LE0ST/Transmisor-FM/simulation/captures/4nec2/[2] Configuración GEOMETRY.png

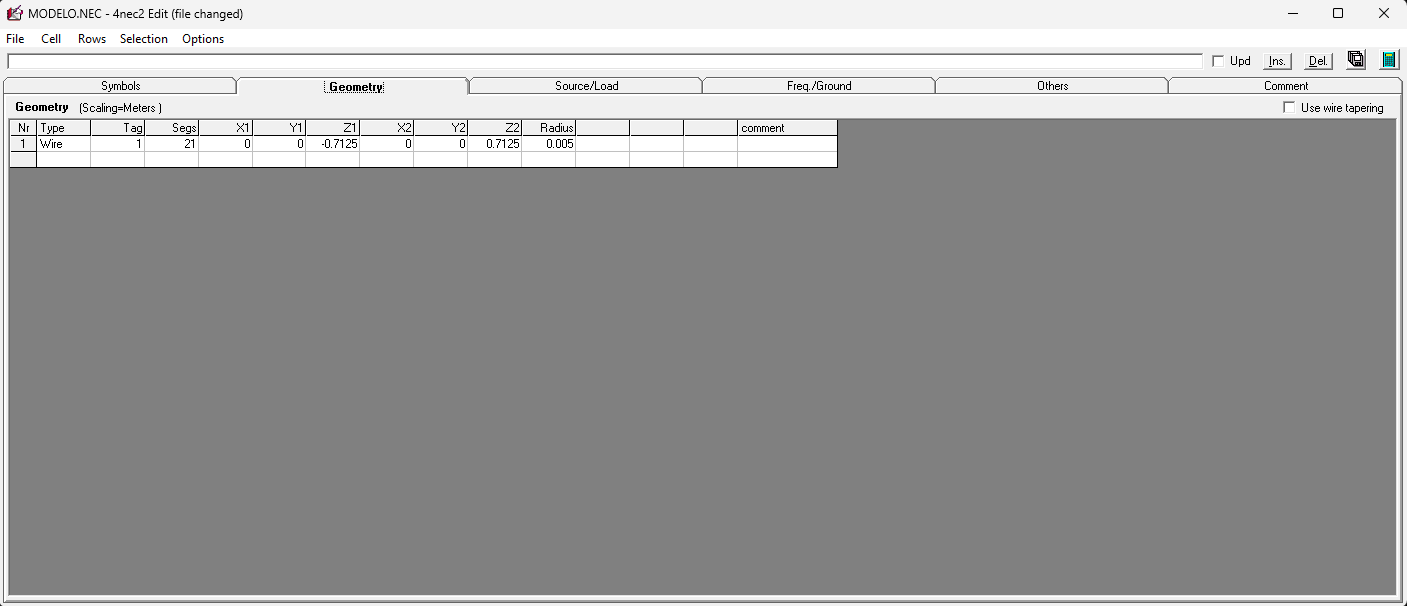
simulation/captures/4nec2/[2] Configuración GEOMETRY.png
