LE0ST/Transmisor-FM/simulation/captures/4nec2/[4] Configuración FREQ_GROUND.png

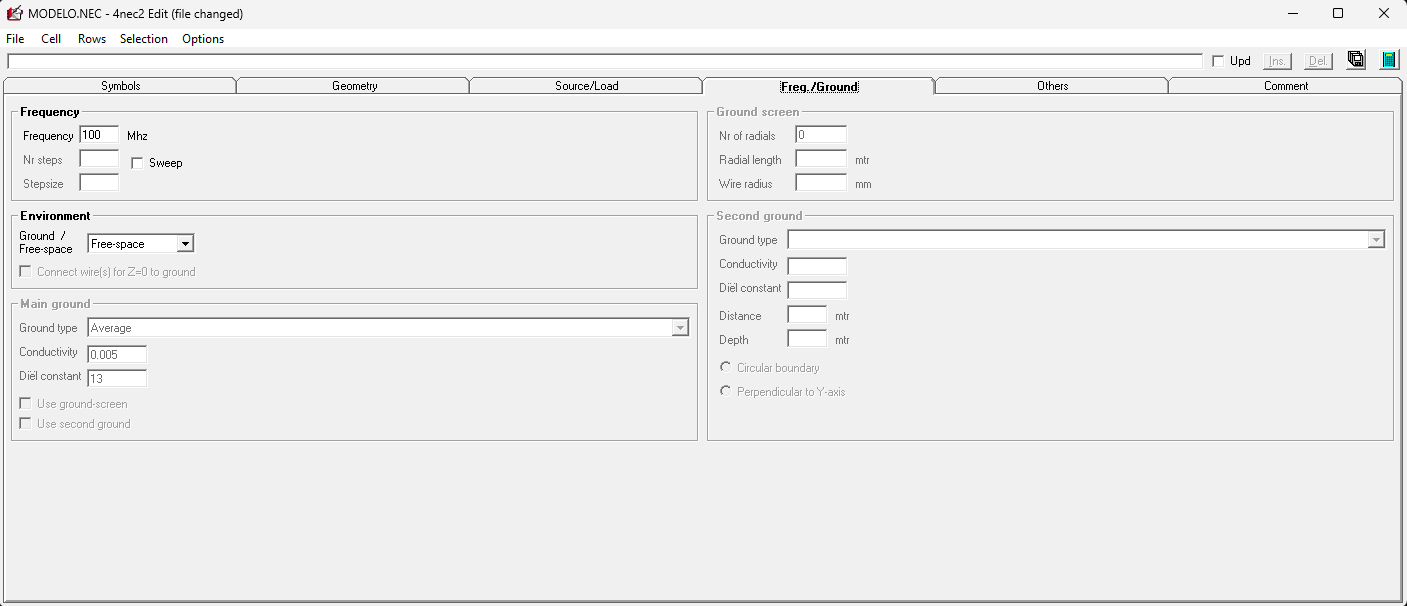
simulation/captures/4nec2/[4] Configuración FREQ_GROUND.png
