LE0ST/Transmisor-FM/simulation/captures/4nec2/[5] Modelo 3D.png

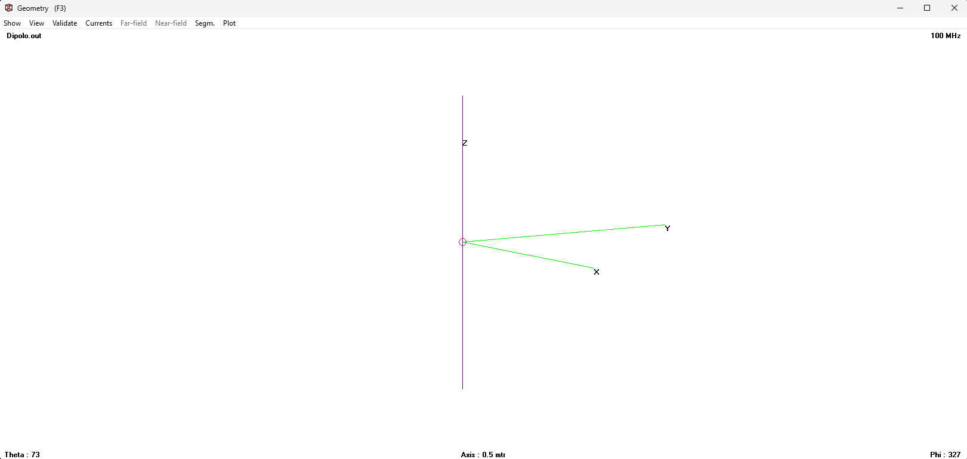
simulation/captures/4nec2/[5] Modelo 3D.png
