LE0ST/Transmisor-FM/simulation/captures/4nec2/[6] Diagrama de Radiación 2D.png

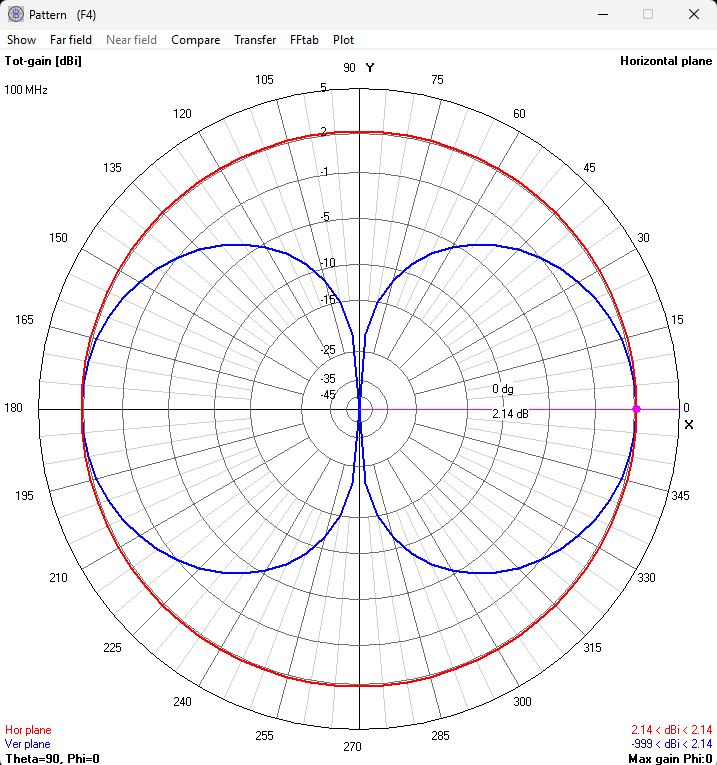
simulation/captures/4nec2/[6] Diagrama de Radiación 2D.png
