LE0ST/Transmisor-FM/simulation/captures/4nec2/[8] Respuesta SWR.png

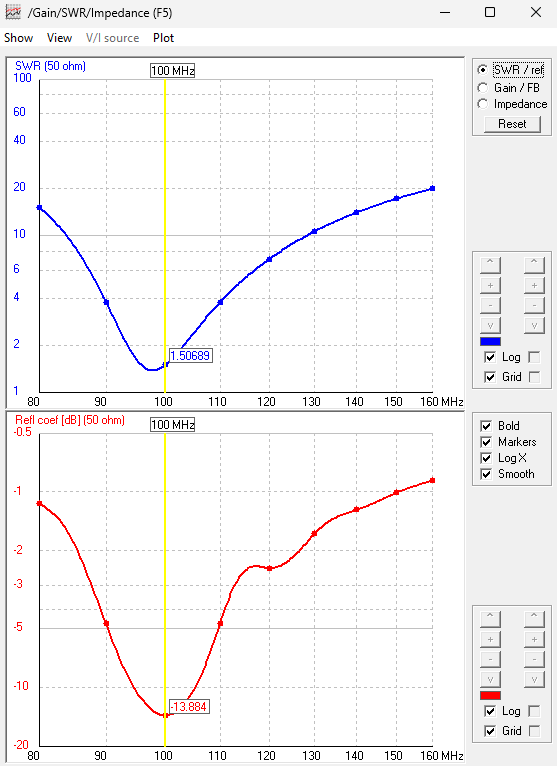
simulation/captures/4nec2/[8] Respuesta SWR.png
