LE0ST/Transmisor-FM/simulation/captures/altium_designer/[3] Altium Library Loader.png

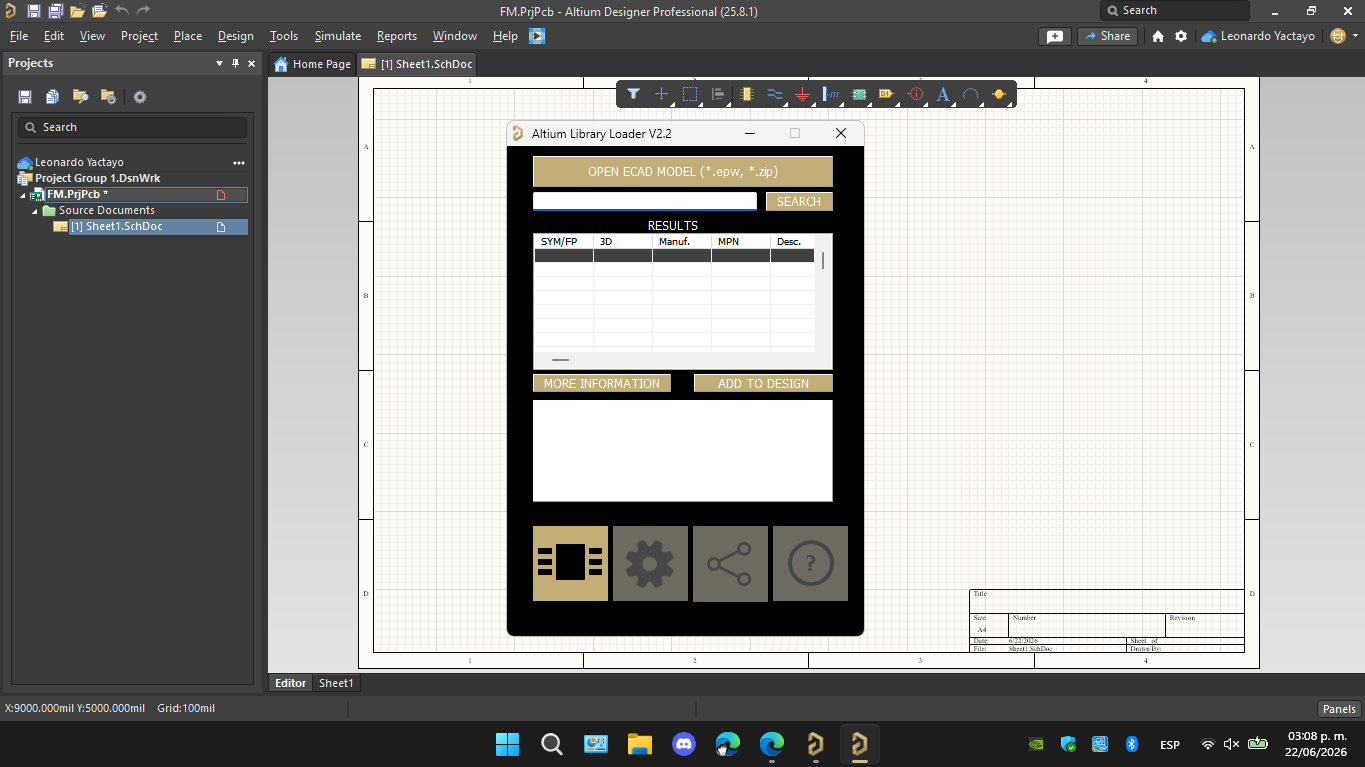
simulation/captures/altium_designer/[3] Altium Library Loader.png
