LE0ST/Transmisor-FM/simulation/captures/altium_designer/[4] Esquemático S9014 S9018.png

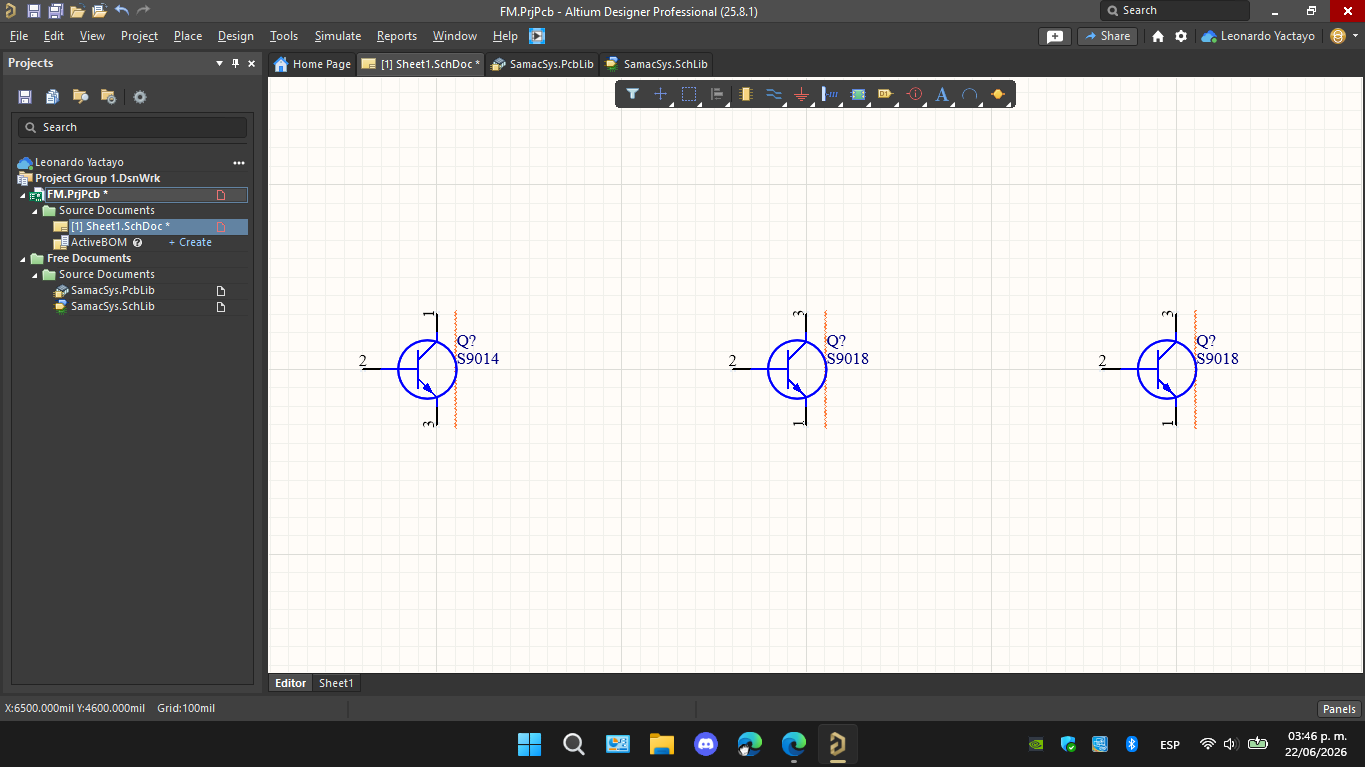
simulation/captures/altium_designer/[4] Esquemático S9014 S9018.png
