LE0ST/Transmisor-FM/simulation/captures/altium_designer/[5] Configuración Fuente AC.png

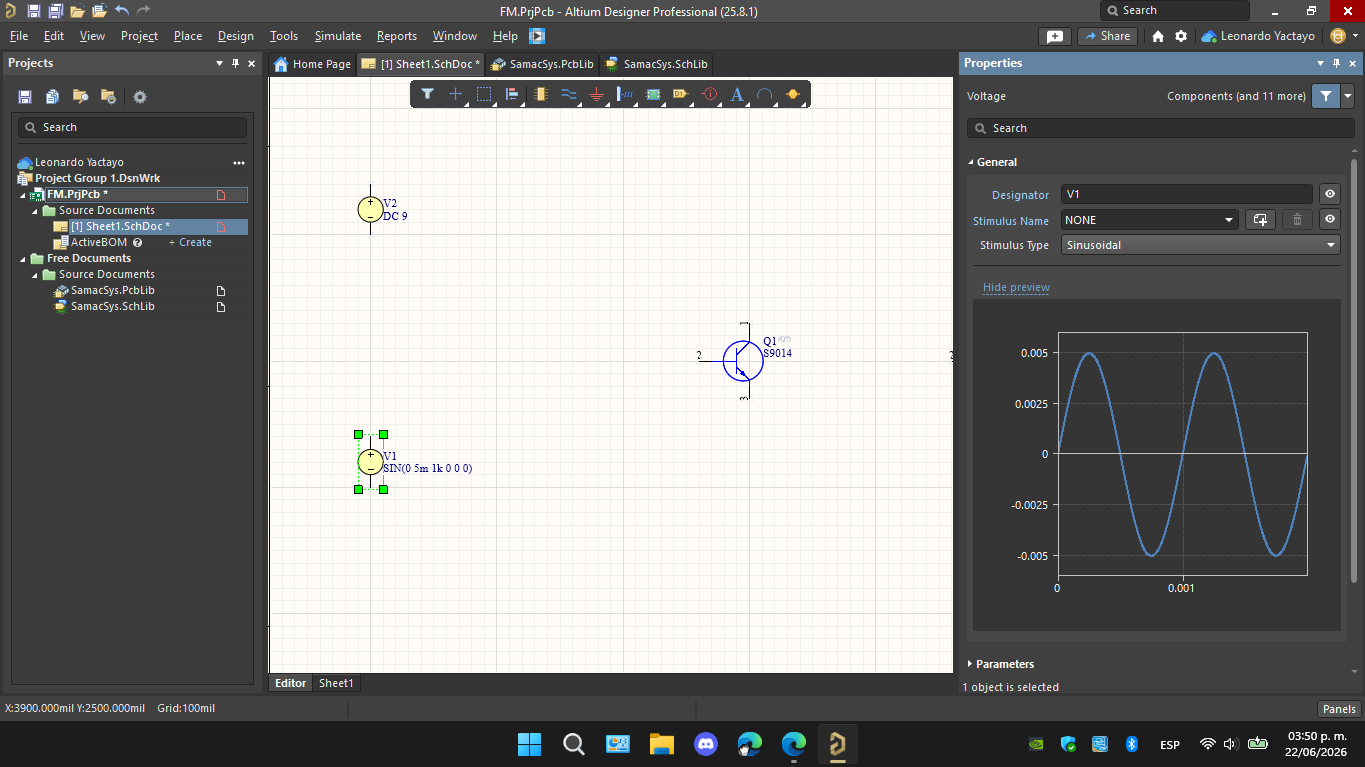
simulation/captures/altium_designer/[5] Configuración Fuente AC.png
