LE0ST/Transmisor-FM/simulation/captures/altium_designer/[9] Creación de Modelo SPICE.png

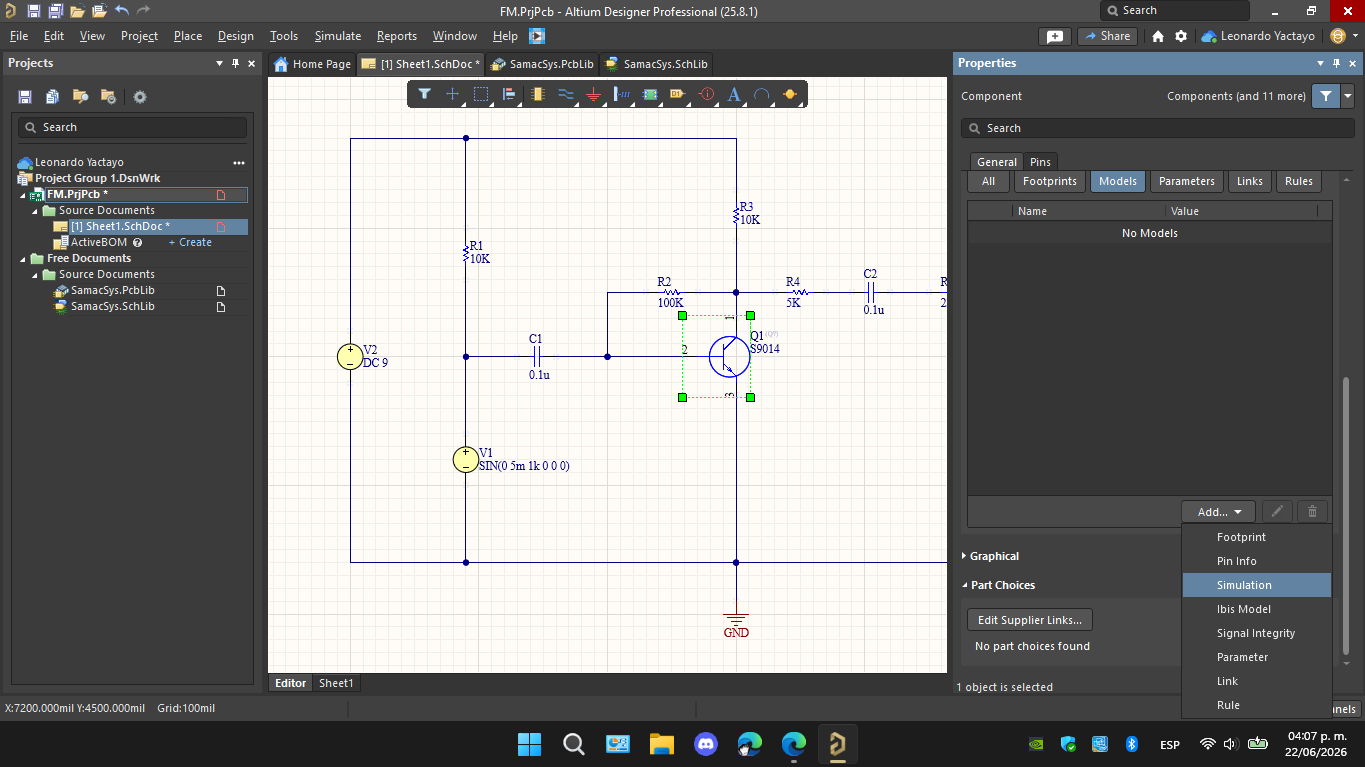
simulation/captures/altium_designer/[9] Creación de Modelo SPICE.png
