LE0ST/Transmisor-FM/simulation/captures/altium_designer/[10] Modelo SPICE S9014.png

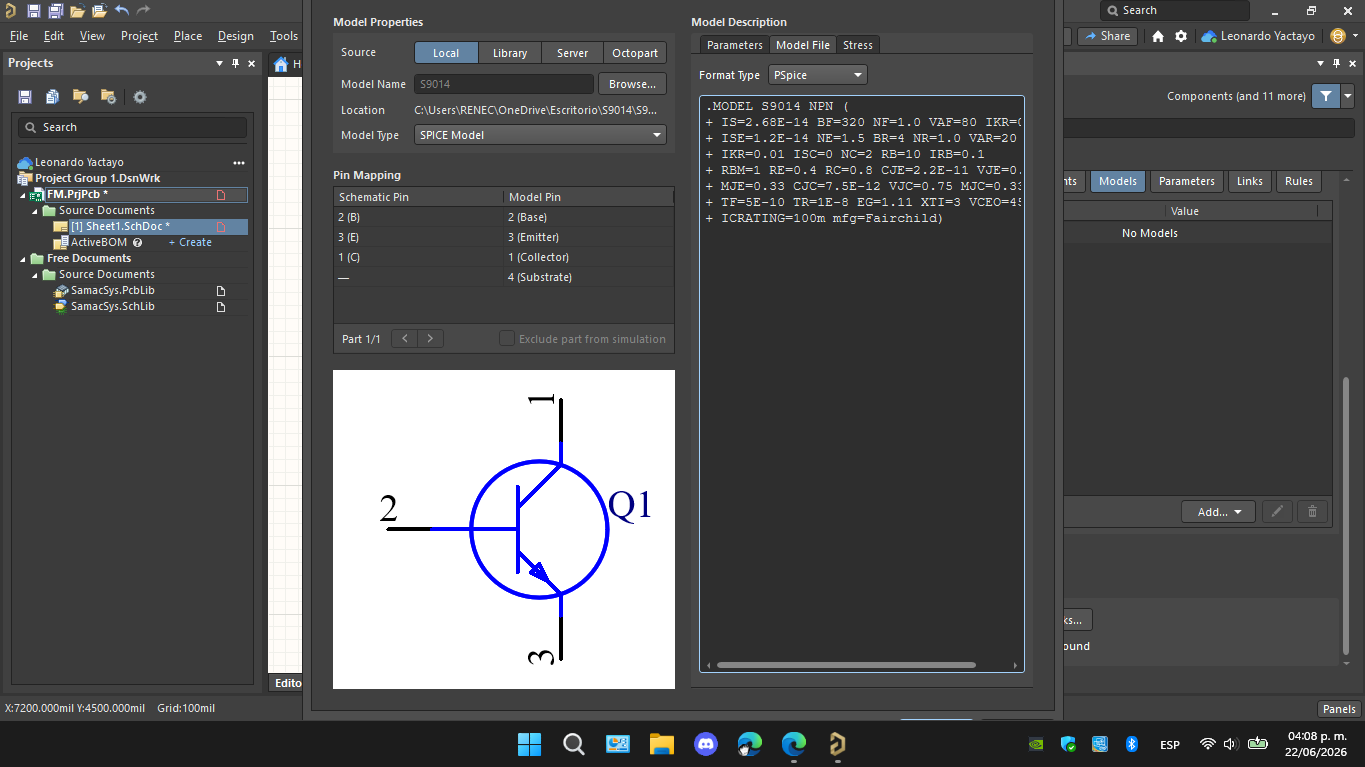
simulation/captures/altium_designer/[10] Modelo SPICE S9014.png
