LE0ST/Transmisor-FM/simulation/captures/altium_designer/[11] Modelo SPICE S9018.png

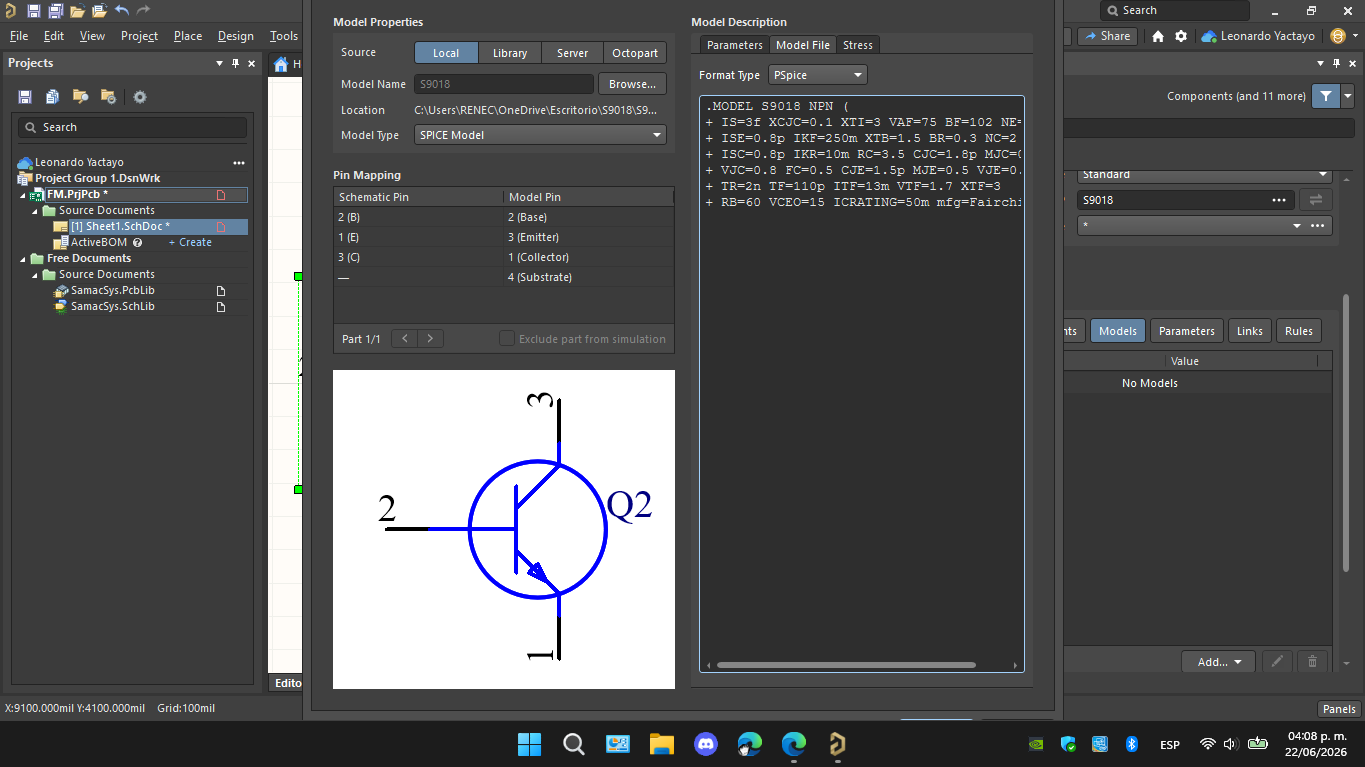
simulation/captures/altium_designer/[11] Modelo SPICE S9018.png
