LE0ST/Transmisor-FM/simulation/captures/altium_designer/[12] Etapa de Amplificación AF.png

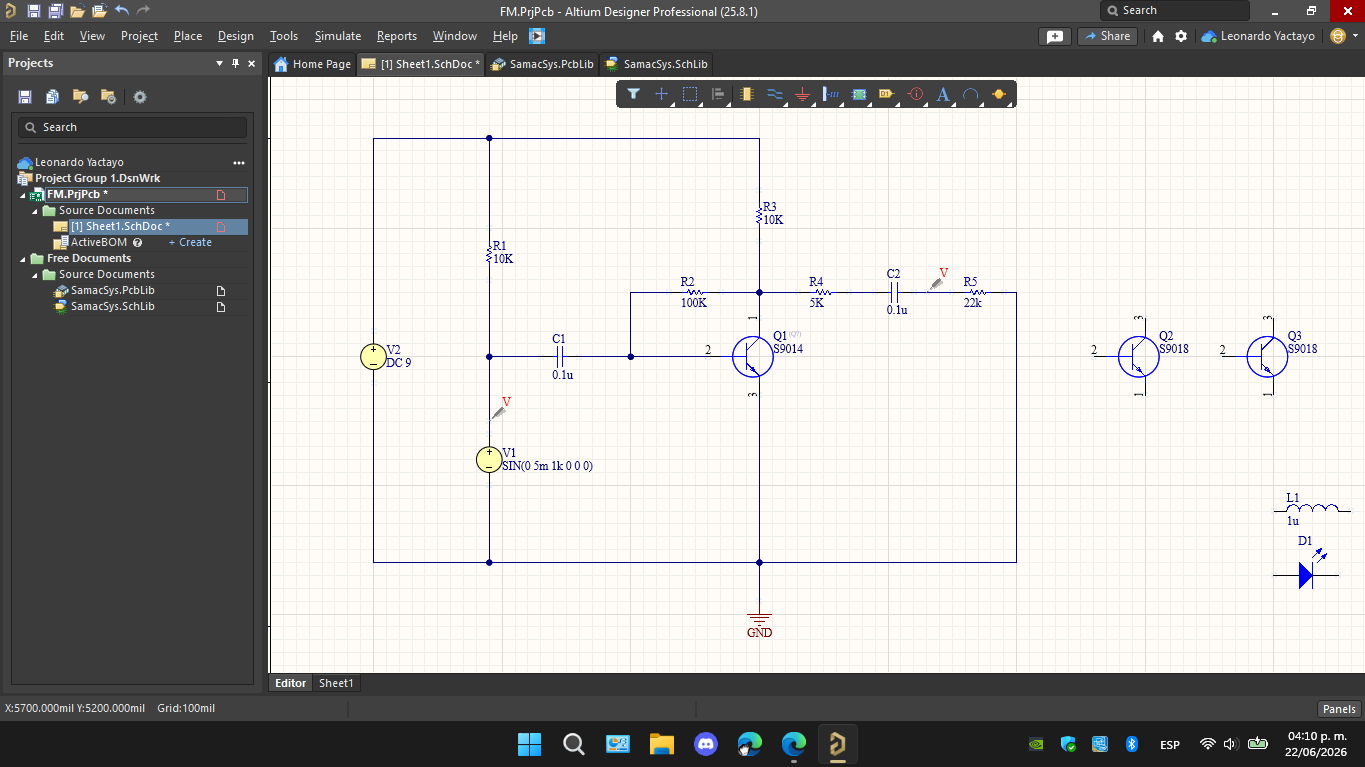
simulation/captures/altium_designer/[12] Etapa de Amplificación AF.png
