LE0ST/Transmisor-FM/simulation/captures/altium_designer/[13] Parámetros TRANSIENT.png

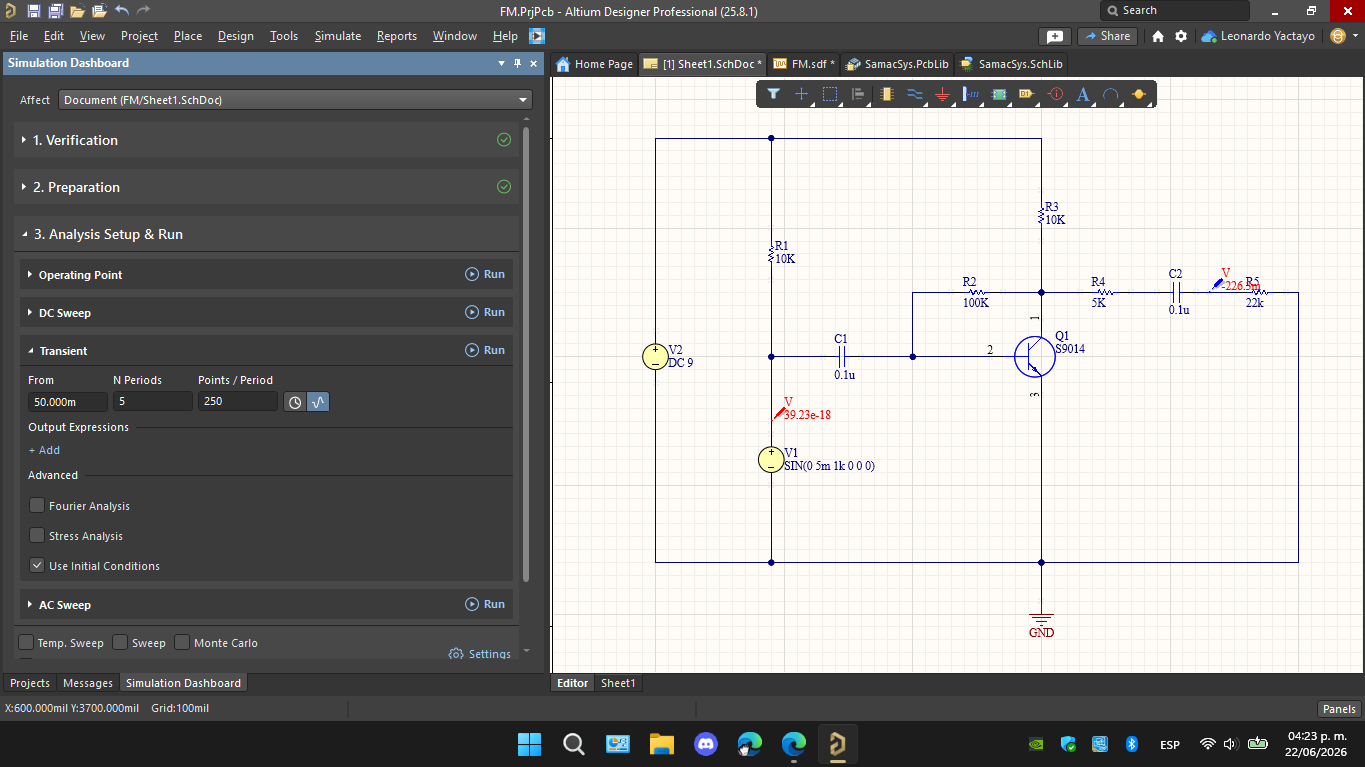
simulation/captures/altium_designer/[13] Parámetros TRANSIENT.png
