LE0ST/Transmisor-FM/simulation/captures/altium_designer/[14] Respuesta TRANSIENT.png

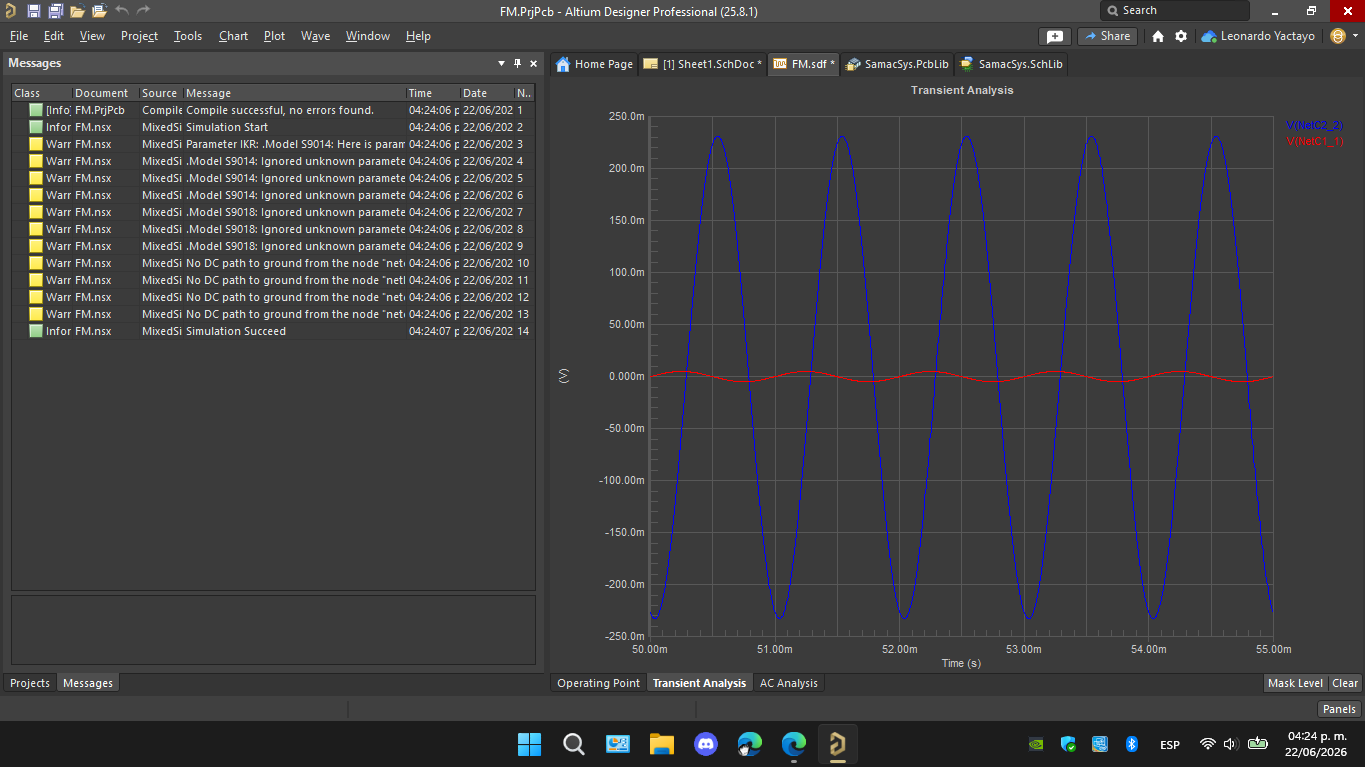
simulation/captures/altium_designer/[14] Respuesta TRANSIENT.png
