LE0ST/Transmisor-FM/simulation/captures/altium_designer/[16] Etapa de Oscilador.png

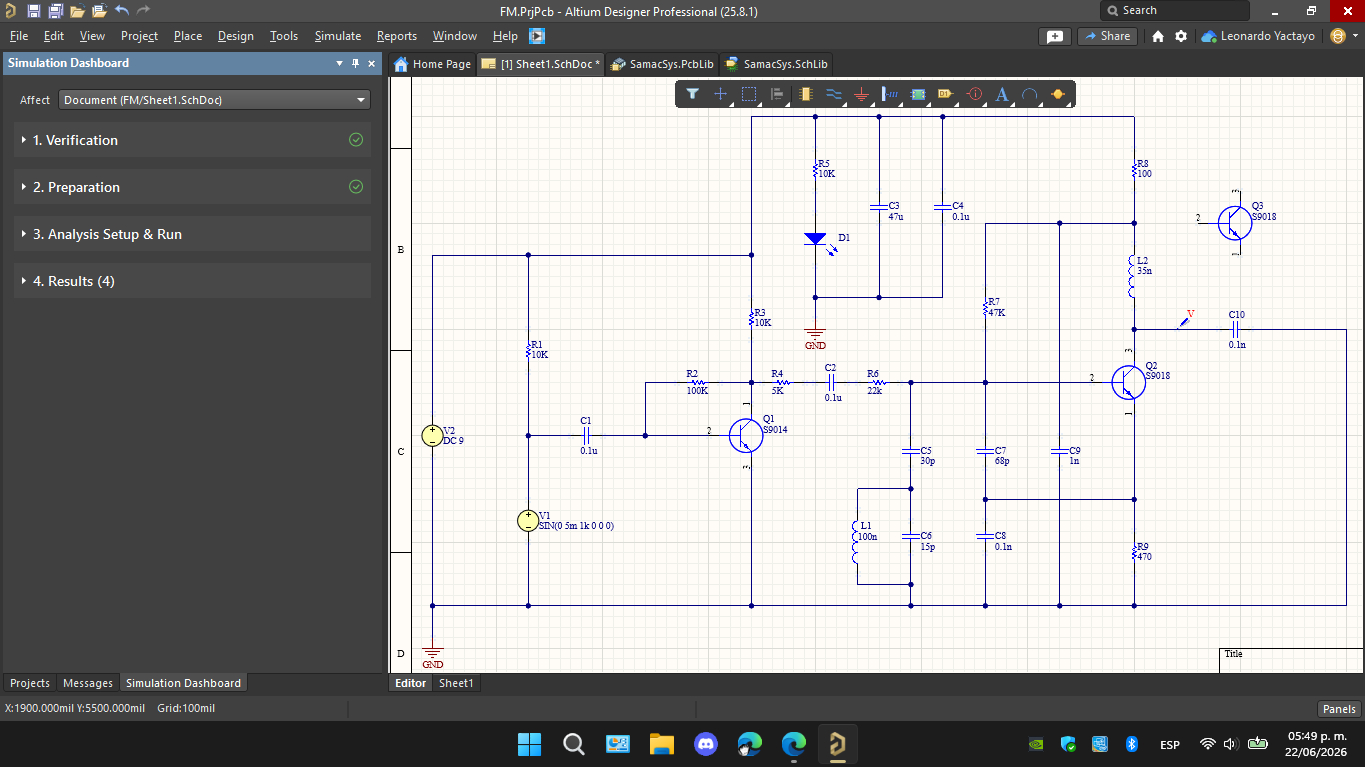
simulation/captures/altium_designer/[16] Etapa de Oscilador.png
