LE0ST/Transmisor-FM/simulation/captures/altium_designer/[20] Respuesta FOURIER.png

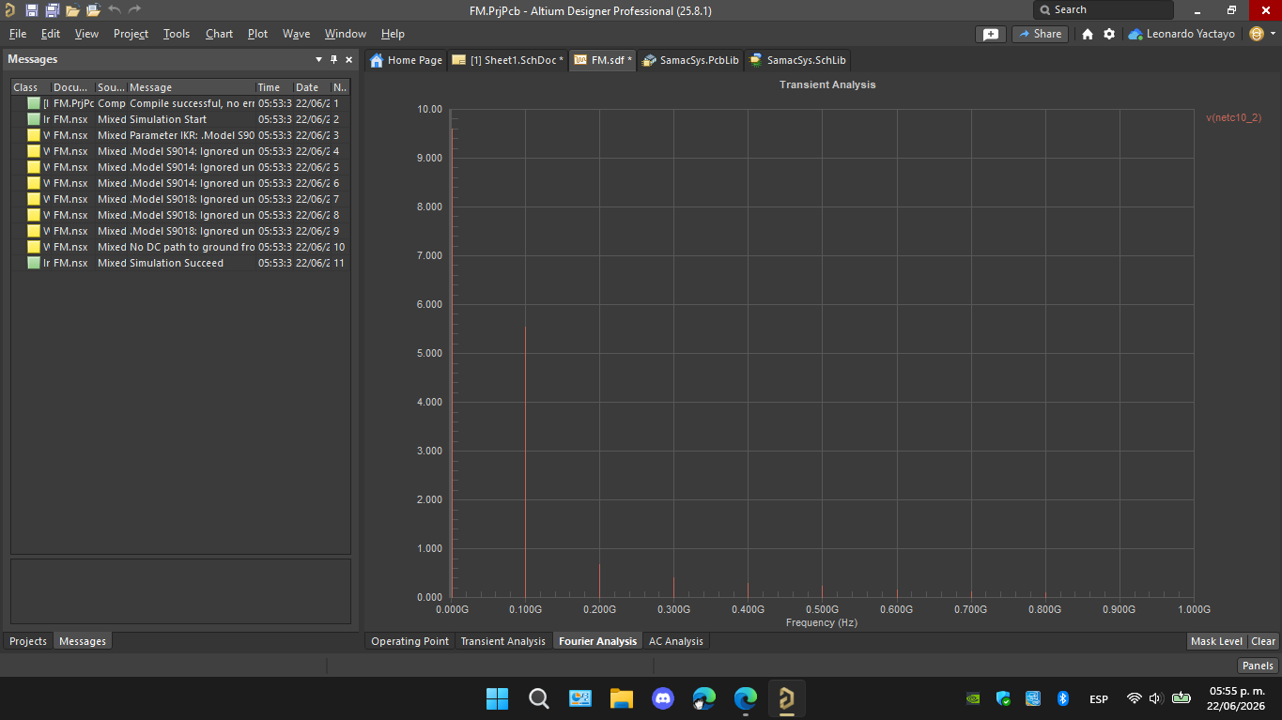
simulation/captures/altium_designer/[20] Respuesta FOURIER.png
