LE0ST/Transmisor-FM/simulation/captures/altium_designer/[28] Etapa Filtro de Acoplamiento.png

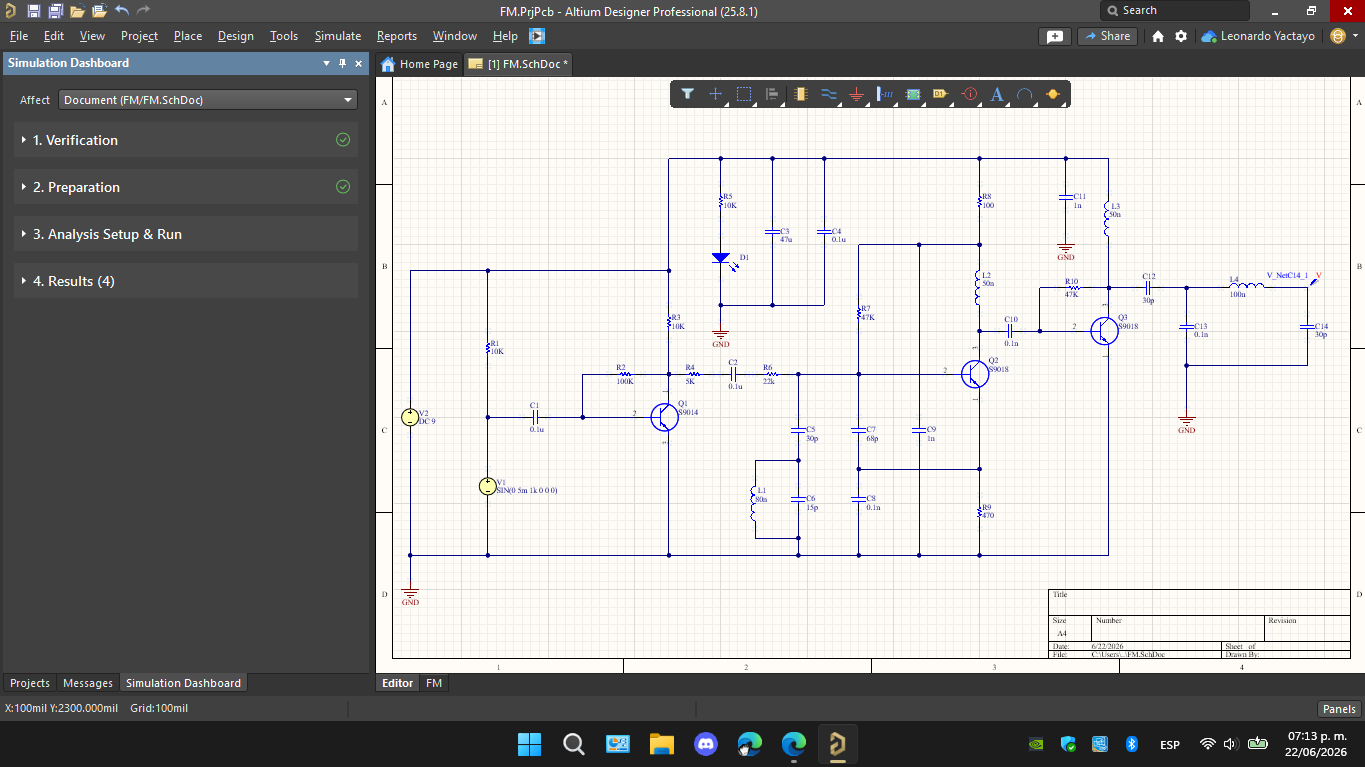
simulation/captures/altium_designer/[28] Etapa Filtro de Acoplamiento.png
