LE0ST/Transmisor-FM/simulation/captures/altium_designer/[30] Parámetros AC SWEEP.png

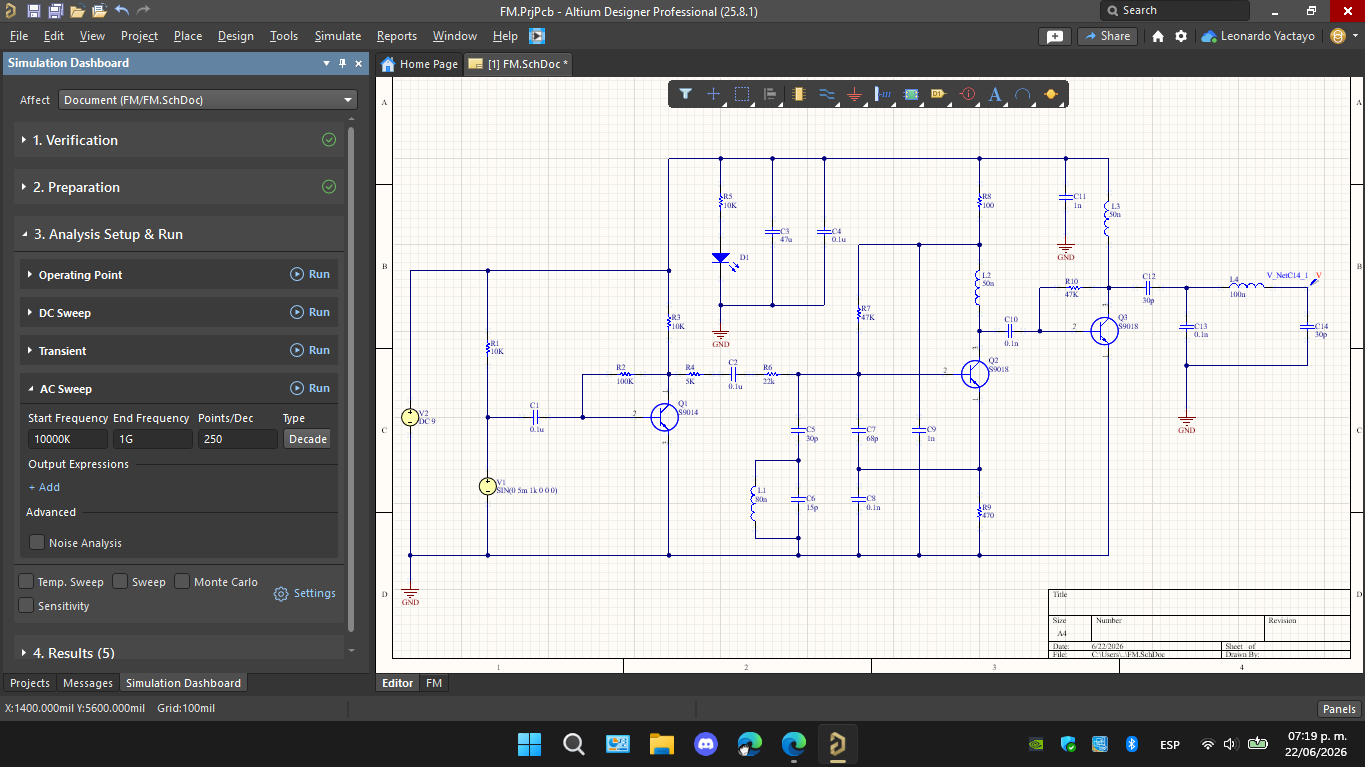
simulation/captures/altium_designer/[30] Parámetros AC SWEEP.png
