LE0ST/Transmisor-FM/simulation/captures/altium_designer/[31] Respuesta TRANSIENT.png

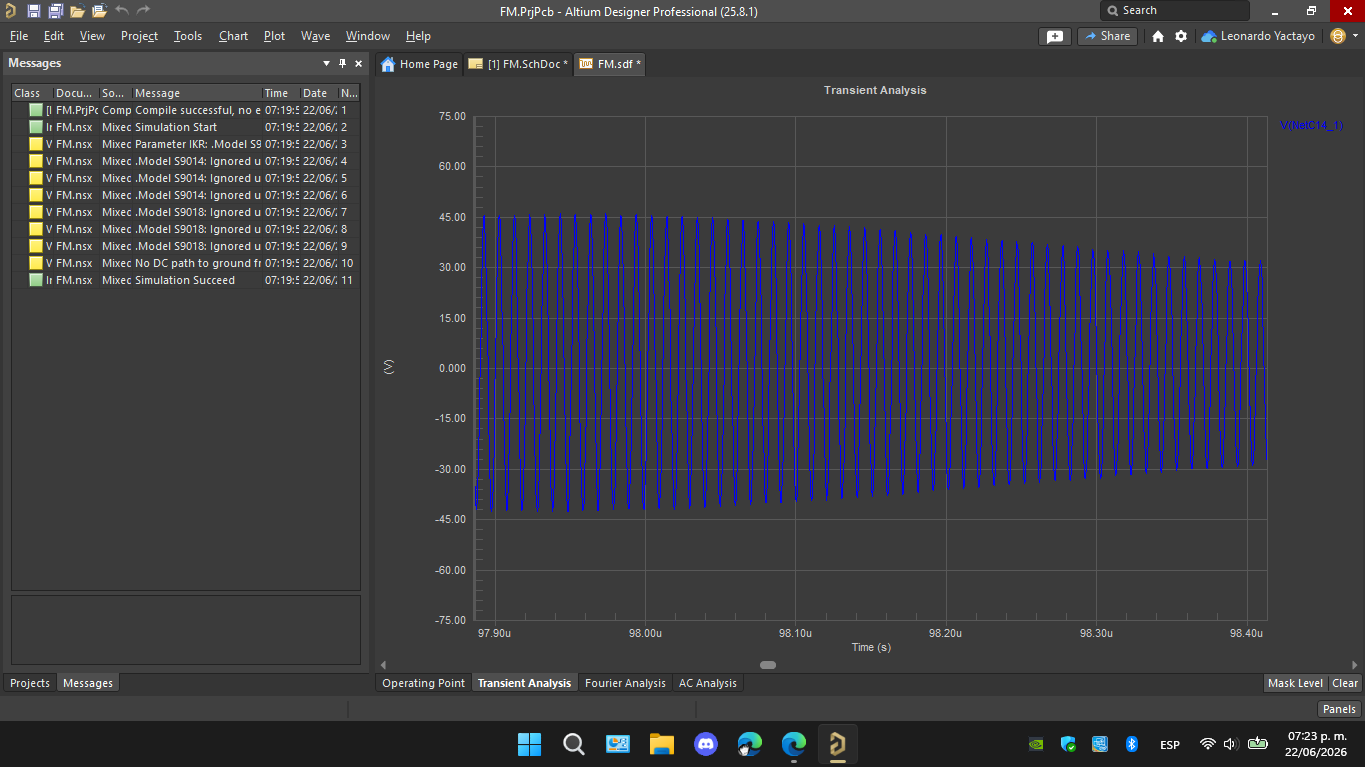
simulation/captures/altium_designer/[31] Respuesta TRANSIENT.png
