LE0ST/Transmisor-FM/simulation/captures/altium_designer/[8] Componentes Generales.png

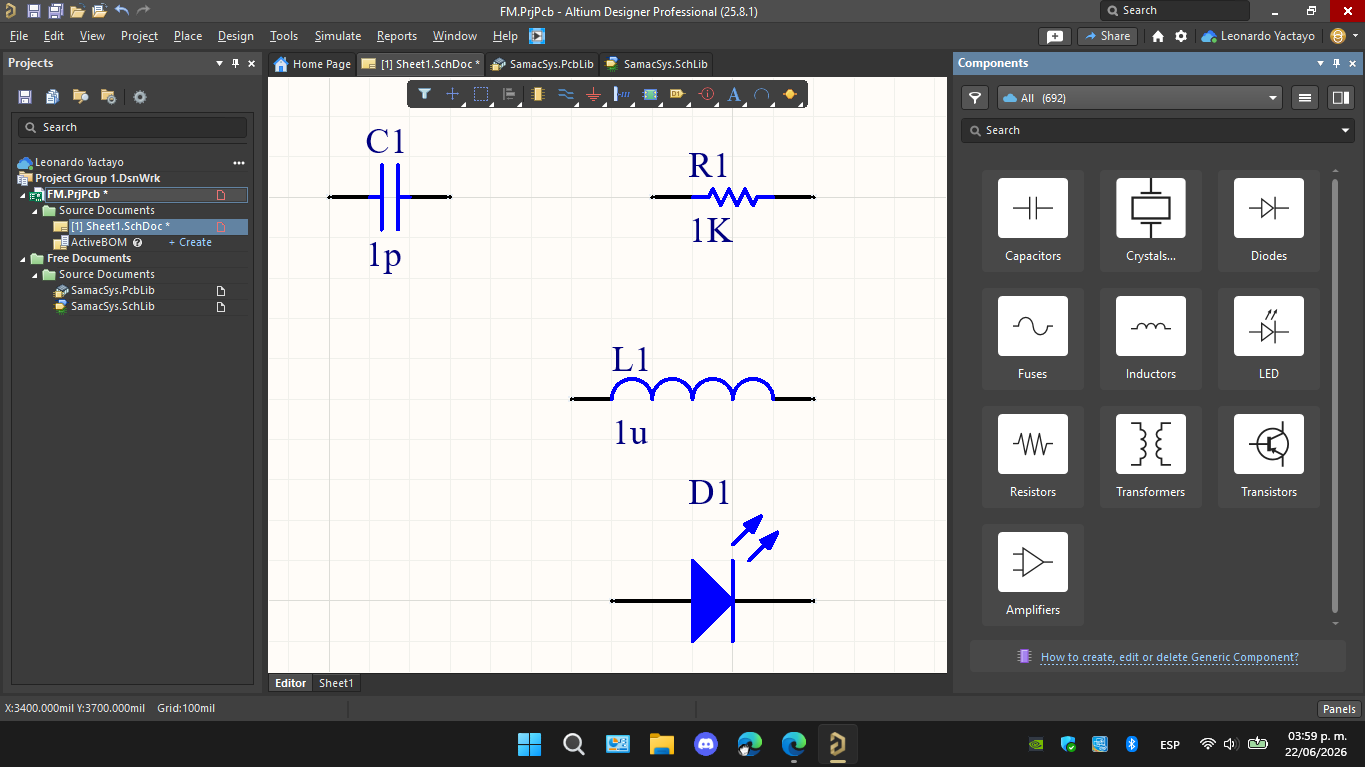
simulation/captures/altium_designer/[8] Componentes Generales.png
